tjhorner/tetris-gamepad/src/main.h

#include <EEPROM.h>
#include "button.h"
#include "pins.h"
#include "config.h"
#include "randmac.h"
#include "modes/mode.h"
#include "modes/gamepad.h"
#include "modes/keyboard.h"
#include "modes/switch.h"
